xpire/flatbox-shift/process/IMG_2580.jpg

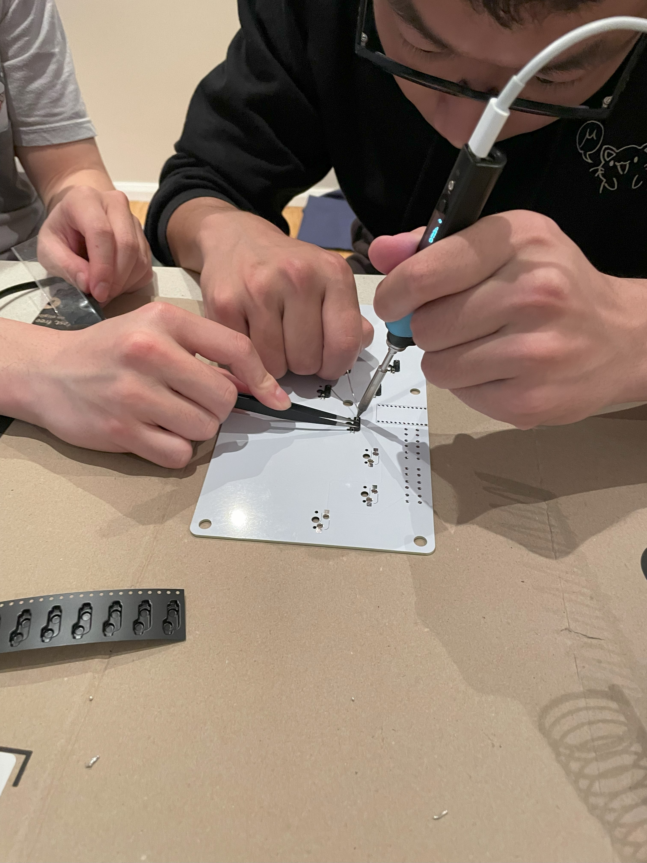
process/IMG_2580.jpg
