xpire/flatbox-shift/process/IMG_2588.jpg

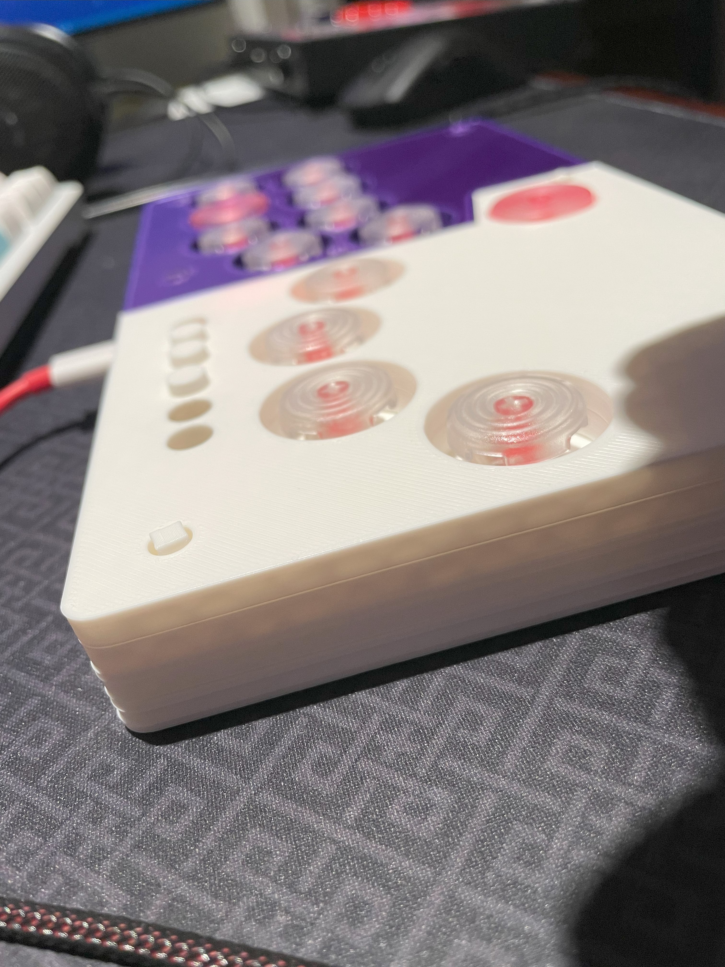
process/IMG_2588.jpg
