xpire/flatbox-shift/process/IMG_5431.jpg

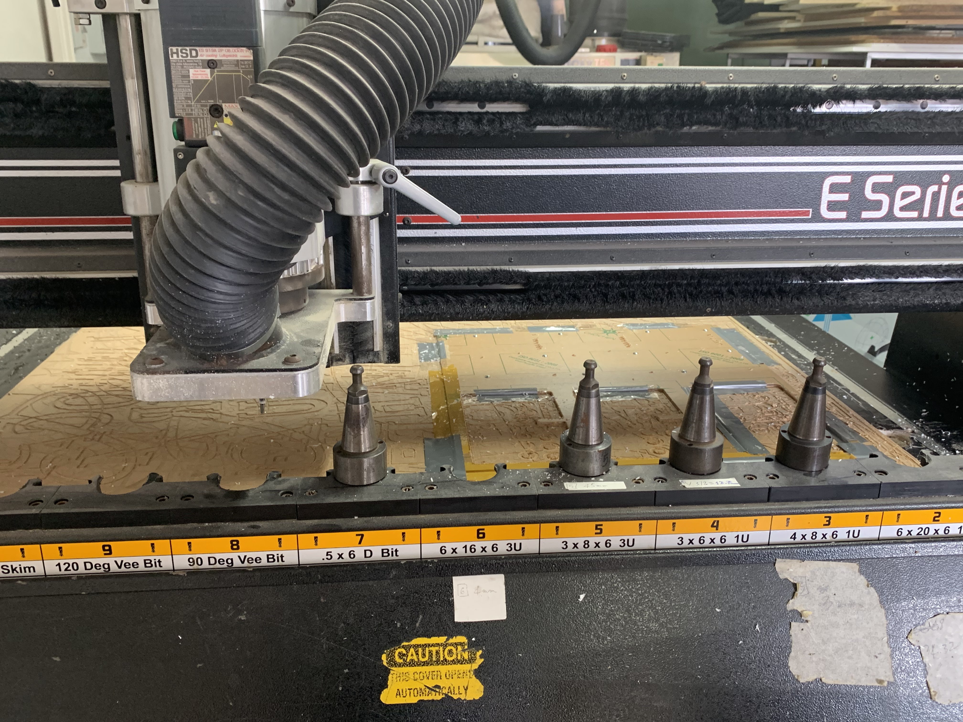
process/IMG_5431.jpg
