xpire/flatbox-shift/process/IMG_5436.jpg

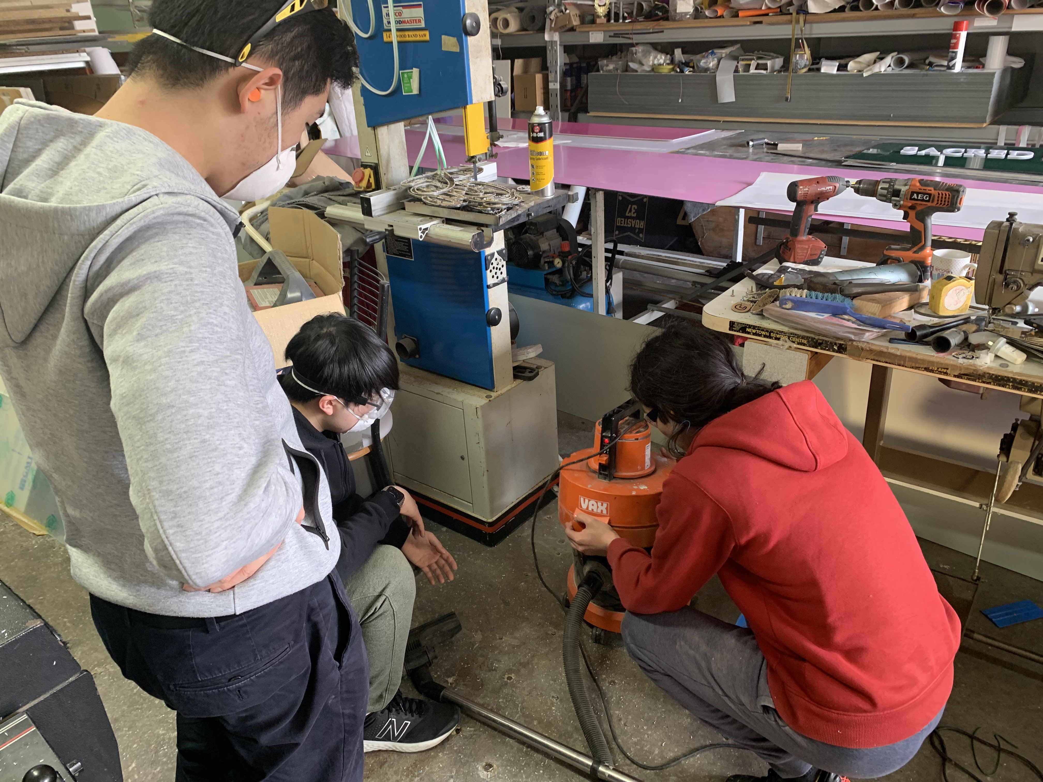
process/IMG_5436.jpg
