xpire/flatbox-shift/result/IMG_2684.jpg

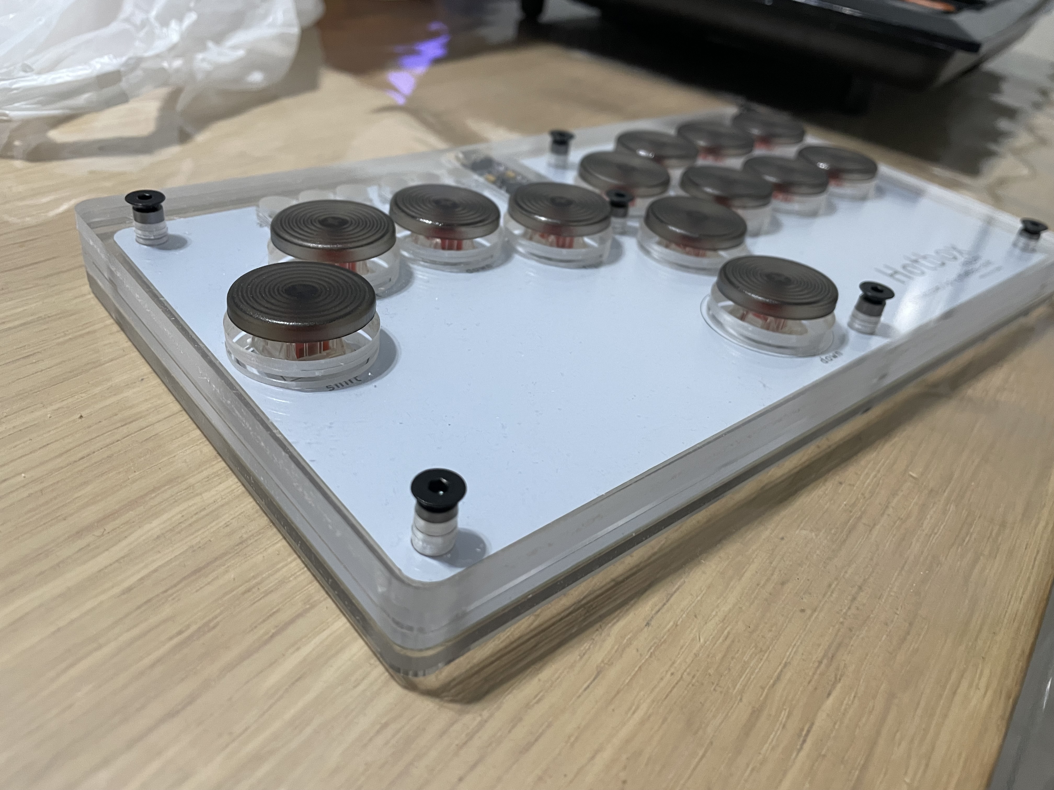
result/IMG_2684.jpg
