xpire/flatbox-shift/result/IMG_2854.jpg

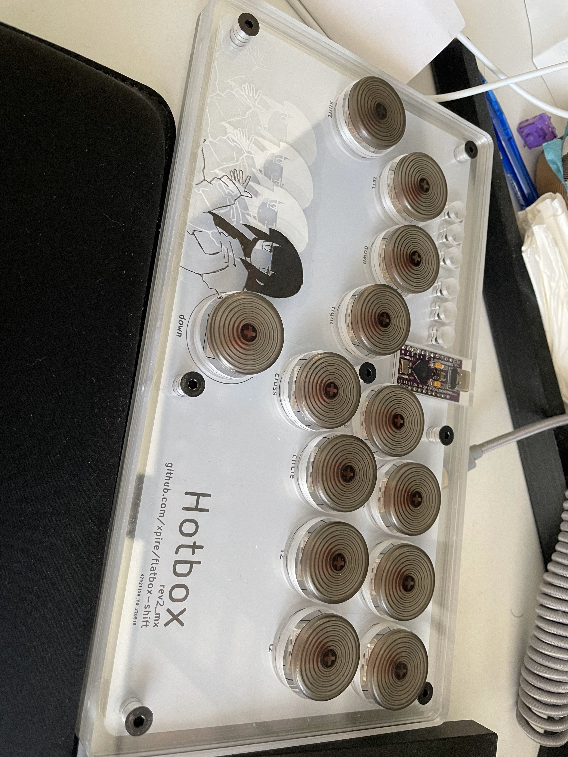
result/IMG_2854.jpg
